neerajadsul/Stagy58/Ortho82Unifiedfirmware/Split82Firmware/Split82Firmware/src/driver_init.c

/**
 * \file
 *
 * \brief Driver initialization.
 *
 (c) 2020 Microchip Technology Inc. and its subsidiaries.

    Subject to your compliance with these terms,you may use this software and
    any derivatives exclusively with Microchip products.It is your responsibility
    to comply with third party license terms applicable to your use of third party
    software (including open source software) that may accompany Microchip software.

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
    IN NO EVENT WILL MICROCHIP BE LIABLE FOR ANY INDIRECT, SPECIAL, PUNITIVE,
    INCIDENTAL OR CONSEQUENTIAL LOSS, DAMAGE, COST OR EXPENSE OF ANY KIND
    WHATSOEVER RELATED TO THE SOFTWARE, HOWEVER CAUSED, EVEN IF MICROCHIP HAS
    BEEN ADVISED OF THE POSSIBILITY OR THE DAMAGES ARE FORESEEABLE. TO THE
    FULLEST EXTENT ALLOWED BY LAW, MICROCHIP'S TOTAL LIABILITY ON ALL CLAIMS IN
    ANY WAY RELATED TO THIS SOFTWARE WILL NOT EXCEED THE AMOUNT OF FEES, IF ANY,
    THAT YOU HAVE PAID DIRECTLY TO MICROCHIP FOR THIS SOFTWARE.
 *
 */

/*
 * Code generated by START.
 *
 * This file will be overwritten when reconfiguring your START project.
 * Please copy examples or other code you want to keep to a separate file
 * to avoid losing it when reconfiguring.
 */

#include "driver_init.h"
#include <system.h>

/* configure pins and initialize registers */
void SLEEP_initialization(void)
{
	SLEEP_init();
}

/* Configure pins and initialize registers */
void USART_KBD_initialization(void)
{

	// Set pin direction to input
	PE2_set_dir(PORT_DIR_IN);

	PE2_set_output_pull_mode(
	    // <y> Output and Pull Configuration
	    // <id> pad_output_pull_config
	    // <PORT_CONFIGURATION_TOTEM"> Totem-pole
	    // <PORT_CONFIGURATION_BUSKEEPER"> Totem-pole with bus-keeper
	    // <PORT_CONFIGURATION_PULLDOWN"> Pull-down
	    // <PORT_CONFIGURATION_PULLUP"> Pull-up
	    // <PORT_CONFIGURATION_WIREDOR"> Wired-OR
	    // <PORT_CONFIGURATION_WIREDAND"> Wired-AND
	    // <PORT_CONFIGURATION_WIREDORPULL"> Wired-OR with pull-down
	    // <PORT_CONFIGURATION_WIREDANDPULL"> Wired-AND with pull-up
	    PORT_CONFIGURATION_TOTEM);

	// Set pin direction to output
	PE3_set_dir(PORT_DIR_OUT);

	PE3_set_level(
	    // <y> Initial level
	    // <id> pad_initial_level
	    // <false"> Low
	    // <true"> High
	    true);

	USART_KBD_init();
}

/* Configure pins and initialize registers */
void USART_USB_initialization(void)
{

	// Set pin direction to input
	PD6_set_dir(PORT_DIR_IN);

	PD6_set_output_pull_mode(
	    // <y> Output and Pull Configuration
	    // <id> pad_output_pull_config
	    // <PORT_CONFIGURATION_TOTEM"> Totem-pole
	    // <PORT_CONFIGURATION_BUSKEEPER"> Totem-pole with bus-keeper
	    // <PORT_CONFIGURATION_PULLDOWN"> Pull-down
	    // <PORT_CONFIGURATION_PULLUP"> Pull-up
	    // <PORT_CONFIGURATION_WIREDOR"> Wired-OR
	    // <PORT_CONFIGURATION_WIREDAND"> Wired-AND
	    // <PORT_CONFIGURATION_WIREDORPULL"> Wired-OR with pull-down
	    // <PORT_CONFIGURATION_WIREDANDPULL"> Wired-AND with pull-up
	    PORT_CONFIGURATION_TOTEM);

	// Set pin direction to output
	PD7_set_dir(PORT_DIR_OUT);

	PD7_set_level(
	    // <y> Initial level
	    // <id> pad_initial_level
	    // <false"> Low
	    // <true"> High
	    false);

	USART_USB_init();
}

/**
 * \brief System initialization
 */
void system_init()
{
	mcu_init();

	/* PORT setting on PB2 */

	// Set pin direction to input
	IS_LEFT_set_dir(PORT_DIR_IN);

	IS_LEFT_set_output_pull_mode(
	    // <y> Output and Pull Configuration
	    // <id> pad_output_pull_config
	    // <PORT_CONFIGURATION_TOTEM"> Totem-pole
	    // <PORT_CONFIGURATION_BUSKEEPER"> Totem-pole with bus-keeper
	    // <PORT_CONFIGURATION_PULLDOWN"> Pull-down
	    // <PORT_CONFIGURATION_PULLUP"> Pull-up
	    // <PORT_CONFIGURATION_WIREDOR"> Wired-OR
	    // <PORT_CONFIGURATION_WIREDAND"> Wired-AND
	    // <PORT_CONFIGURATION_WIREDORPULL"> Wired-OR with pull-down
	    // <PORT_CONFIGURATION_WIREDANDPULL"> Wired-AND with pull-up
	    PORT_CONFIGURATION_TOTEM);

	/* PORT setting on PB3 */

	// Set pin direction to output
	USER_LED_set_dir(PORT_DIR_OUT);

	USER_LED_set_level(
	    // <y> Initial level
	    // <id> pad_initial_level
	    // <false"> Low
	    // <true"> High
	    false);

	/* PORT setting on PC0 */

	// Set pin direction to output
	COL_0_set_dir(PORT_DIR_OUT);

	COL_0_set_level(
	    // <y> Initial level
	    // <id> pad_initial_level
	    // <false"> Low
	    // <true"> High
	    false);

	/* PORT setting on PC1 */

	// Set pin direction to output
	COL_1_set_dir(PORT_DIR_OUT);

	COL_1_set_level(
	    // <y> Initial level
	    // <id> pad_initial_level
	    // <false"> Low
	    // <true"> High
	    true);

	/* PORT setting on PC2 */

	// Set pin direction to output
	COL_2_set_dir(PORT_DIR_OUT);

	COL_2_set_level(
	    // <y> Initial level
	    // <id> pad_initial_level
	    // <false"> Low
	    // <true"> High
	    false);

	/* PORT setting on PC3 */

	// Set pin direction to output
	COL_3_set_dir(PORT_DIR_OUT);

	COL_3_set_level(
	    // <y> Initial level
	    // <id> pad_initial_level
	    // <false"> Low
	    // <true"> High
	    false);

	/* PORT setting on PC4 */

	// Set pin direction to output
	COL_4_set_dir(PORT_DIR_OUT);

	COL_4_set_level(
	    // <y> Initial level
	    // <id> pad_initial_level
	    // <false"> Low
	    // <true"> High
	    false);

	/* PORT setting on PC5 */

	// Set pin direction to output
	COL_5_set_dir(PORT_DIR_OUT);

	COL_5_set_level(
	    // <y> Initial level
	    // <id> pad_initial_level
	    // <false"> Low
	    // <true"> High
	    false);

	/* PORT setting on PC6 */

	// Set pin direction to output
	COL_6_set_dir(PORT_DIR_OUT);

	COL_6_set_level(
	    // <y> Initial level
	    // <id> pad_initial_level
	    // <false"> Low
	    // <true"> High
	    false);

	/* PORT setting on PD0 */

	// Set pin direction to input
	ROW_0_set_dir(PORT_DIR_IN);

	ROW_0_set_output_pull_mode(
	    // <y> Output and Pull Configuration
	    // <id> pad_output_pull_config
	    // <PORT_CONFIGURATION_TOTEM"> Totem-pole
	    // <PORT_CONFIGURATION_BUSKEEPER"> Totem-pole with bus-keeper
	    // <PORT_CONFIGURATION_PULLDOWN"> Pull-down
	    // <PORT_CONFIGURATION_PULLUP"> Pull-up
	    // <PORT_CONFIGURATION_WIREDOR"> Wired-OR
	    // <PORT_CONFIGURATION_WIREDAND"> Wired-AND
	    // <PORT_CONFIGURATION_WIREDORPULL"> Wired-OR with pull-down
	    // <PORT_CONFIGURATION_WIREDANDPULL"> Wired-AND with pull-up
	    PORT_CONFIGURATION_PULLDOWN);

	/* PORT setting on PD1 */

	// Set pin direction to input
	ROW_1_set_dir(PORT_DIR_IN);

	ROW_1_set_output_pull_mode(
	    // <y> Output and Pull Configuration
	    // <id> pad_output_pull_config
	    // <PORT_CONFIGURATION_TOTEM"> Totem-pole
	    // <PORT_CONFIGURATION_BUSKEEPER"> Totem-pole with bus-keeper
	    // <PORT_CONFIGURATION_PULLDOWN"> Pull-down
	    // <PORT_CONFIGURATION_PULLUP"> Pull-up
	    // <PORT_CONFIGURATION_WIREDOR"> Wired-OR
	    // <PORT_CONFIGURATION_WIREDAND"> Wired-AND
	    // <PORT_CONFIGURATION_WIREDORPULL"> Wired-OR with pull-down
	    // <PORT_CONFIGURATION_WIREDANDPULL"> Wired-AND with pull-up
	    PORT_CONFIGURATION_PULLDOWN);

	/* PORT setting on PD2 */

	// Set pin direction to input
	ROW_2_set_dir(PORT_DIR_IN);

	ROW_2_set_output_pull_mode(
	    // <y> Output and Pull Configuration
	    // <id> pad_output_pull_config
	    // <PORT_CONFIGURATION_TOTEM"> Totem-pole
	    // <PORT_CONFIGURATION_BUSKEEPER"> Totem-pole with bus-keeper
	    // <PORT_CONFIGURATION_PULLDOWN"> Pull-down
	    // <PORT_CONFIGURATION_PULLUP"> Pull-up
	    // <PORT_CONFIGURATION_WIREDOR"> Wired-OR
	    // <PORT_CONFIGURATION_WIREDAND"> Wired-AND
	    // <PORT_CONFIGURATION_WIREDORPULL"> Wired-OR with pull-down
	    // <PORT_CONFIGURATION_WIREDANDPULL"> Wired-AND with pull-up
	    PORT_CONFIGURATION_PULLDOWN);

	/* PORT setting on PD3 */

	// Set pin direction to input
	ROW_3_set_dir(PORT_DIR_IN);

	ROW_3_set_output_pull_mode(
	    // <y> Output and Pull Configuration
	    // <id> pad_output_pull_config
	    // <PORT_CONFIGURATION_TOTEM"> Totem-pole
	    // <PORT_CONFIGURATION_BUSKEEPER"> Totem-pole with bus-keeper
	    // <PORT_CONFIGURATION_PULLDOWN"> Pull-down
	    // <PORT_CONFIGURATION_PULLUP"> Pull-up
	    // <PORT_CONFIGURATION_WIREDOR"> Wired-OR
	    // <PORT_CONFIGURATION_WIREDAND"> Wired-AND
	    // <PORT_CONFIGURATION_WIREDORPULL"> Wired-OR with pull-down
	    // <PORT_CONFIGURATION_WIREDANDPULL"> Wired-AND with pull-up
	    PORT_CONFIGURATION_PULLDOWN);

	/* PORT setting on PD4 */

	// Set pin direction to input
	ROW_4_set_dir(PORT_DIR_IN);

	ROW_4_set_output_pull_mode(
	    // <y> Output and Pull Configuration
	    // <id> pad_output_pull_config
	    // <PORT_CONFIGURATION_TOTEM"> Totem-pole
	    // <PORT_CONFIGURATION_BUSKEEPER"> Totem-pole with bus-keeper
	    // <PORT_CONFIGURATION_PULLDOWN"> Pull-down
	    // <PORT_CONFIGURATION_PULLUP"> Pull-up
	    // <PORT_CONFIGURATION_WIREDOR"> Wired-OR
	    // <PORT_CONFIGURATION_WIREDAND"> Wired-AND
	    // <PORT_CONFIGURATION_WIREDORPULL"> Wired-OR with pull-down
	    // <PORT_CONFIGURATION_WIREDANDPULL"> Wired-AND with pull-up
	    PORT_CONFIGURATION_PULLDOWN);

	/* PORT setting on PD5 */

	// Set pin direction to input
	ROW_F_set_dir(PORT_DIR_IN);

	ROW_F_set_output_pull_mode(
	    // <y> Output and Pull Configuration
	    // <id> pad_output_pull_config
	    // <PORT_CONFIGURATION_TOTEM"> Totem-pole
	    // <PORT_CONFIGURATION_BUSKEEPER"> Totem-pole with bus-keeper
	    // <PORT_CONFIGURATION_PULLDOWN"> Pull-down
	    // <PORT_CONFIGURATION_PULLUP"> Pull-up
	    // <PORT_CONFIGURATION_WIREDOR"> Wired-OR
	    // <PORT_CONFIGURATION_WIREDAND"> Wired-AND
	    // <PORT_CONFIGURATION_WIREDORPULL"> Wired-OR with pull-down
	    // <PORT_CONFIGURATION_WIREDANDPULL"> Wired-AND with pull-up
	    PORT_CONFIGURATION_PULLDOWN);

	OSC_init();

	CLK_init();

	PMIC_init();

	SLEEP_initialization();

	USART_KBD_initialization();

	USART_USB_initialization();
}
