neerajadsul/Stagy58/Ortho82Unifiedfirmware/Split82Firmware/Split82Firmware/src/usart_basic.c

/**
 * \file
 *
 * \brief USART basic driver.
 *
 (c) 2020 Microchip Technology Inc. and its subsidiaries.

    Subject to your compliance with these terms,you may use this software and
    any derivatives exclusively with Microchip products.It is your responsibility
    to comply with third party license terms applicable to your use of third party
    software (including open source software) that may accompany Microchip software.

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
    IN NO EVENT WILL MICROCHIP BE LIABLE FOR ANY INDIRECT, SPECIAL, PUNITIVE,
    INCIDENTAL OR CONSEQUENTIAL LOSS, DAMAGE, COST OR EXPENSE OF ANY KIND
    WHATSOEVER RELATED TO THE SOFTWARE, HOWEVER CAUSED, EVEN IF MICROCHIP HAS
    BEEN ADVISED OF THE POSSIBILITY OR THE DAMAGES ARE FORESEEABLE. TO THE
    FULLEST EXTENT ALLOWED BY LAW, MICROCHIP'S TOTAL LIABILITY ON ALL CLAIMS IN
    ANY WAY RELATED TO THIS SOFTWARE WILL NOT EXCEED THE AMOUNT OF FEES, IF ANY,
    THAT YOU HAVE PAID DIRECTLY TO MICROCHIP FOR THIS SOFTWARE.
 *
 */

/**
 * \defgroup doc_driver_usart_basic USART Basic
 * \ingroup doc_driver_usart
 *
 * \section doc_driver_usart_basic_rev Revision History
 * - v0.0.0.1 Initial Commit
 *
 *@{
 */
#include <compiler.h>
#include <clock_config.h>
#include <usart_basic.h>
#include <atomic.h>

/* Static Variables holding the ringbuffer used in IRQ mode */
static uint8_t          USART_KBD_rxbuf[USART_KBD_RX_BUFFER_SIZE];
static volatile uint8_t USART_KBD_rx_head;
static volatile uint8_t USART_KBD_rx_tail;
static volatile uint8_t USART_KBD_rx_elements;
static uint8_t          USART_KBD_txbuf[USART_KBD_TX_BUFFER_SIZE];
static volatile uint8_t USART_KBD_tx_head;
static volatile uint8_t USART_KBD_tx_tail;
static volatile uint8_t USART_KBD_tx_elements;

void USART_KBD_default_rx_isr_cb(void);
void (*USART_KBD_rx_isr_cb)(void) = &USART_KBD_default_rx_isr_cb;
void USART_KBD_default_udre_isr_cb(void);
void (*USART_KBD_udre_isr_cb)(void) = &USART_KBD_default_udre_isr_cb;

void USART_KBD_default_rx_isr_cb(void)
{
	uint8_t data;
	uint8_t tmphead;

	/* Read the received data */
	data = USARTE0.DATA;
	/* Calculate buffer index */
	tmphead = (USART_KBD_rx_head + 1) & USART_KBD_RX_BUFFER_MASK;

	if (tmphead == USART_KBD_rx_tail) {
		/* ERROR! Receive buffer overflow */
	} else {
		/* Store new index */
		USART_KBD_rx_head = tmphead;

		/* Store received data in buffer */
		USART_KBD_rxbuf[tmphead] = data;
		USART_KBD_rx_elements++;
	}
}

void USART_KBD_default_udre_isr_cb(void)
{
	uint8_t tmptail;

	/* Check if all data is transmitted */
	if (USART_KBD_tx_elements != 0) {
		/* Calculate buffer index */
		tmptail = (USART_KBD_tx_tail + 1) & USART_KBD_TX_BUFFER_MASK;
		/* Store new index */
		USART_KBD_tx_tail = tmptail;
		/* Start transmission */
		USARTE0.DATA = USART_KBD_txbuf[tmptail];
		USART_KBD_tx_elements--;
	}

	if (USART_KBD_tx_elements == 0) {
		/* Disable UDRE interrupt */
		USARTE0.CTRLA &= ~(USART_DREINTLVL_gm);
	}
}

/**
 * \brief Set call back function for USART_KBD
 *
 * \param[in] cb The call back function to set
 *
 * \param[in] type The type of ISR to be set
 *
 * \return Nothing
 */
void USART_KBD_set_ISR_cb(usart_cb_t cb, usart_cb_type_t type)
{
	switch (type) {
	case RX_CB:
		USART_KBD_rx_isr_cb = cb;
		break;
	case UDRE_CB:
		USART_KBD_udre_isr_cb = cb;
		break;
	default:
		// do nothing
		break;
	}
}

/* Interrupt service routine for RX complete */
ISR(USARTE0_RXC_vect)
{
	if (USART_KBD_rx_isr_cb != NULL)
		(*USART_KBD_rx_isr_cb)();
}

/* Interrupt service routine for Data Register Empty */
ISR(USARTE0_DRE_vect)
{
	if (USART_KBD_udre_isr_cb != NULL)
		(*USART_KBD_udre_isr_cb)();
}

bool USART_KBD_is_tx_ready()
{
	return (USART_KBD_tx_elements != USART_KBD_TX_BUFFER_SIZE);
}

bool USART_KBD_is_rx_ready()
{
	return (USART_KBD_rx_elements != 0);
}

bool USART_KBD_is_tx_busy()
{
	return (!(USARTE0.STATUS & USART_TXCIF_bm));
}

/**
 * \brief Read one character from USART_KBD
 *
 * Function will block if a character is not available.
 *
 * \return Data read from the USART_KBD module
 */
uint8_t USART_KBD_read(void)
{
	uint8_t tmptail;

	/* Wait for incoming data */
	while (USART_KBD_rx_elements == 0)
		;
	/* Calculate buffer index */
	tmptail = (USART_KBD_rx_tail + 1) & USART_KBD_RX_BUFFER_MASK;
	/* Store new index */
	USART_KBD_rx_tail = tmptail;
	ENTER_CRITICAL(R);
	USART_KBD_rx_elements--;
	EXIT_CRITICAL(R);

	/* Return data */
	return USART_KBD_rxbuf[tmptail];
}

/**
 * \brief Write one character to USART_KBD
 *
 * Function will block until a character can be accepted.
 *
 * \param[in] data The character to write to the USART
 *
 * \return Nothing
 */
void USART_KBD_write(const uint8_t data)
{
	uint8_t tmphead;

	/* Calculate buffer index */
	tmphead = (USART_KBD_tx_head + 1) & USART_KBD_TX_BUFFER_MASK;
	/* Wait for free space in buffer */
	while (USART_KBD_tx_elements == USART_KBD_TX_BUFFER_SIZE)
		;
	/* Store data in buffer */
	USART_KBD_txbuf[tmphead] = data;
	/* Store new index */
	USART_KBD_tx_head = tmphead;
	ENTER_CRITICAL(W);
	USART_KBD_tx_elements++;
	EXIT_CRITICAL(W);
	/* Enable UDRE interrupt */
	USARTE0.CTRLA |= USART_DREINTLVL_LO_gc;
}

/**
 * \brief Initialize USART interface
 * If module is configured to disabled state, the clock to the USART is disabled
 * if this is supported by the device's clock system.
 *
 * \return Initialization status.
 * \retval 0 the USART init was successful
 * \retval 1 the USART init was not successful
 */
int8_t USART_KBD_init()
{

	int8_t   exp;
	uint32_t div;
	uint32_t limit;
	uint32_t ratio;
	uint32_t min_rate;
	uint32_t max_rate;

	uint32_t cpu_hz = F_CPU;
	uint32_t baud   = 115200;

	/*
	 * Check if the hardware supports the given baud rate
	 */
	/* 8 = (2^0) * 8 * (2^0) = (2^BSCALE_MIN) * 8 * (BSEL_MIN) */
	max_rate = cpu_hz / 8;
	/* 4194304 = (2^7) * 8 * (2^12) = (2^BSCALE_MAX) * 8 * (BSEL_MAX+1) */
	min_rate = cpu_hz / 4194304;

	/* double speed is disabled. */
	max_rate /= 2;
	min_rate /= 2;

	if ((baud > max_rate) || (baud < min_rate)) {
		/* the hardware doesn't supports the given baud rate */
		return -1;
	}

	/* double speed is disabled. */
	baud *= 2;

	/* Find the lowest possible exponent. */
	limit = 0xfffU >> 4;
	ratio = cpu_hz / baud;

	for (exp = -7; exp < 7; exp++) {
		if (ratio < limit) {
			break;
		}

		limit <<= 1;

		if (exp < -3) {
			limit |= 1;
		}
	}

	/*
	 * Depending on the value of exp, scale either the input frequency or
	 * the target baud rate. By always scaling upwards, we never introduce
	 * any additional inaccuracy.
	 *
	 * We are including the final divide-by-8 (aka. right-shift-by-3) in
	 * this operation as it ensures that we never exceeed 2**32 at any
	 * point.
	 *
	 * The formula for calculating BSEL is slightly different when exp is
	 * negative than it is when exp is positive.
	 */
	if (exp < 0) {
		/* We are supposed to subtract 1, then apply BSCALE. We want to
		 * apply BSCALE first, so we need to turn everything inside the
		 * parenthesis into a single fractional expression.
		 */
		cpu_hz -= 8 * baud;

		/* If we end up with a left-shift after taking the final
		 * divide-by-8 into account, do the shift before the divide.
		 * Otherwise, left-shift the denominator instead (effectively
		 * resulting in an overall right shift.)
		 */
		if (exp <= -3) {
			div = ((cpu_hz << (-exp - 3)) + baud / 2) / baud;
		} else {
			baud <<= exp + 3;
			div = (cpu_hz + baud / 2) / baud;
		}
	} else {
		/* We will always do a right shift in this case, but we need to
		 * shift three extra positions because of the divide-by-8.
		 */
		baud <<= exp + 3;
		div = (cpu_hz + baud / 2) / baud - 1;
	}

	USARTE0.BAUDCTRLB = (uint8_t)(((div >> 8) & 0X0F) | (exp << 4));
	USARTE0.BAUDCTRLA = (uint8_t)div;

	USARTE0.CTRLA = USART_RXCINTLVL_LO_gc    /* Low Level */
	                | USART_TXCINTLVL_OFF_gc /* Off */
	                | USART_DREINTLVL_LO_gc; /* Low Level */

	// USARTE0.CTRLC = USART_PMODE_DISABLED_gc /* No Parity */
	//		 | 0 << USART_SBMODE_bp /* Stop Bit Mode: disabled */
	//		 | USART_CHSIZE_8BIT_gc /* Character size: 8 bit */
	//		 | 0 << USART_CHSIZE2_bp /* SPI Master Mode, Data Order: disabled */
	//		 | 1 << USART_CHSIZE1_bp /* SPI Master Mode, Clock Phase: enabled */
	//		 | USART_CMODE_ASYNCHRONOUS_gc; /* Async IRQ Mode */

	USARTE0.CTRLB = 0 << USART_CLK2X_bp   /* Double transmission speed: disabled */
	                | 0 << USART_MPCM_bp  /* Multi-processor Communication Mode: disabled */
	                | 1 << USART_RXEN_bp  /* Receiver Enable: enabled */
	                | 1 << USART_TXEN_bp; /* Transmitter Enable: enabled */

	uint8_t x;

	/* Initialize ringbuffers */
	x = 0;

	USART_KBD_rx_tail     = x;
	USART_KBD_rx_head     = x;
	USART_KBD_rx_elements = x;
	USART_KBD_tx_tail     = x;
	USART_KBD_tx_head     = x;
	USART_KBD_tx_elements = x;

	return 0;
}

/**
 * \brief Enable RX and TX in USART_KBD
 * 1. If supported by the clock system, enables the clock to the USART
 * 2. Enables the USART module by setting the RX and TX enable-bits in the USART control register
 *
 * \return Nothing
 */
void USART_KBD_enable()
{
	USARTE0.CTRLB |= USART_RXEN_bm | USART_TXEN_bm;
}

/**
 * \brief Enable RX in USART_KBD
 * 1. If supported by the clock system, enables the clock to the USART
 * 2. Enables the USART module by setting the RX enable-bit in the USART control register
 *
 * \return Nothing
 */
void USART_KBD_enable_rx()
{
	USARTE0.CTRLB |= USART_RXEN_bm;
}

/**
 * \brief Enable TX in USART_KBD
 * 1. If supported by the clock system, enables the clock to the USART
 * 2. Enables the USART module by setting the TX enable-bit in the USART control register
 *
 * \return Nothing
 */
void USART_KBD_enable_tx()
{
	USARTE0.CTRLB |= USART_TXEN_bm;
}

/**
 * \brief Disable USART_KBD
 * 1. Disables the USART module by clearing the enable-bit(s) in the USART control register
 * 2. If supported by the clock system, disables the clock to the USART
 *
 * \return Nothing
 */
void USART_KBD_disable()
{
	USARTE0.CTRLB &= ~(USART_RXEN_bm | USART_TXEN_bm);
}

/**
 * \brief Get recieved data from USART_KBD
 *
 * \return Data register from USART_KBD module
 */
uint8_t USART_KBD_get_data()
{
	return USARTE0.DATA;
}

#include <stdio.h>

#if defined(__GNUC__)

int USART_USB_printCHAR(char character, FILE *stream)
{
	USART_USB_write(character);
	return 0;
}

FILE USART_USB_stream = FDEV_SETUP_STREAM(USART_USB_printCHAR, NULL, _FDEV_SETUP_WRITE);

#elif defined(__ICCAVR__)

int putchar(int outChar)
{
	USART_0_write(outChar);
	return outChar;
}
#endif

/**
 * \brief Initialize USART interface
 * If module is configured to disabled state, the clock to the USART is disabled
 * if this is supported by the device's clock system.
 *
 * \return Initialization status.
 * \retval 0 the USART init was successful
 * \retval 1 the USART init was not successful
 */
int8_t USART_USB_init()
{

	int8_t   exp;
	uint32_t div;
	uint32_t limit;
	uint32_t ratio;
	uint32_t min_rate;
	uint32_t max_rate;

	uint32_t cpu_hz = F_CPU;
	uint32_t baud   = 9600;

	/*
	 * Check if the hardware supports the given baud rate
	 */
	/* 8 = (2^0) * 8 * (2^0) = (2^BSCALE_MIN) * 8 * (BSEL_MIN) */
	max_rate = cpu_hz / 8;
	/* 4194304 = (2^7) * 8 * (2^12) = (2^BSCALE_MAX) * 8 * (BSEL_MAX+1) */
	min_rate = cpu_hz / 4194304;

	/* double speed is disabled. */
	max_rate /= 2;
	min_rate /= 2;

	if ((baud > max_rate) || (baud < min_rate)) {
		/* the hardware doesn't supports the given baud rate */
		return -1;
	}

	/* double speed is disabled. */
	baud *= 2;

	/* Find the lowest possible exponent. */
	limit = 0xfffU >> 4;
	ratio = cpu_hz / baud;

	for (exp = -7; exp < 7; exp++) {
		if (ratio < limit) {
			break;
		}

		limit <<= 1;

		if (exp < -3) {
			limit |= 1;
		}
	}

	/*
	 * Depending on the value of exp, scale either the input frequency or
	 * the target baud rate. By always scaling upwards, we never introduce
	 * any additional inaccuracy.
	 *
	 * We are including the final divide-by-8 (aka. right-shift-by-3) in
	 * this operation as it ensures that we never exceeed 2**32 at any
	 * point.
	 *
	 * The formula for calculating BSEL is slightly different when exp is
	 * negative than it is when exp is positive.
	 */
	if (exp < 0) {
		/* We are supposed to subtract 1, then apply BSCALE. We want to
		 * apply BSCALE first, so we need to turn everything inside the
		 * parenthesis into a single fractional expression.
		 */
		cpu_hz -= 8 * baud;

		/* If we end up with a left-shift after taking the final
		 * divide-by-8 into account, do the shift before the divide.
		 * Otherwise, left-shift the denominator instead (effectively
		 * resulting in an overall right shift.)
		 */
		if (exp <= -3) {
			div = ((cpu_hz << (-exp - 3)) + baud / 2) / baud;
		} else {
			baud <<= exp + 3;
			div = (cpu_hz + baud / 2) / baud;
		}
	} else {
		/* We will always do a right shift in this case, but we need to
		 * shift three extra positions because of the divide-by-8.
		 */
		baud <<= exp + 3;
		div = (cpu_hz + baud / 2) / baud - 1;
	}

	USARTD1.BAUDCTRLB = (uint8_t)(((div >> 8) & 0X0F) | (exp << 4));
	USARTD1.BAUDCTRLA = (uint8_t)div;

	// USARTD1.CTRLC = USART_PMODE_DISABLED_gc /* No Parity */
	//		 | 0 << USART_SBMODE_bp /* Stop Bit Mode: disabled */
	//		 | USART_CHSIZE_8BIT_gc /* Character size: 8 bit */
	//		 | 0 << USART_CHSIZE2_bp /* SPI Master Mode, Data Order: disabled */
	//		 | 1 << USART_CHSIZE1_bp /* SPI Master Mode, Clock Phase: enabled */
	//		 | USART_CMODE_ASYNCHRONOUS_gc; /* Async Polled Mode */

	USARTD1.CTRLB = 0 << USART_CLK2X_bp   /* Double transmission speed: disabled */
	                | 0 << USART_MPCM_bp  /* Multi-processor Communication Mode: disabled */
	                | 1 << USART_RXEN_bp  /* Receiver Enable: enabled */
	                | 1 << USART_TXEN_bp; /* Transmitter Enable: enabled */

#if defined(__GNUC__)
	stdout = &USART_USB_stream;
#endif

	return 0;
}

/**
 * \brief Enable RX and TX in USART_USB
 * 1. If supported by the clock system, enables the clock to the USART
 * 2. Enables the USART module by setting the RX and TX enable-bits in the USART control register
 *
 * \return Nothing
 */
void USART_USB_enable()
{
	USARTD1.CTRLB |= USART_RXEN_bm | USART_TXEN_bm;
}

/**
 * \brief Enable RX in USART_USB
 * 1. If supported by the clock system, enables the clock to the USART
 * 2. Enables the USART module by setting the RX enable-bit in the USART control register
 *
 * \return Nothing
 */
void USART_USB_enable_rx()
{
	USARTD1.CTRLB |= USART_RXEN_bm;
}

/**
 * \brief Enable TX in USART_USB
 * 1. If supported by the clock system, enables the clock to the USART
 * 2. Enables the USART module by setting the TX enable-bit in the USART control register
 *
 * \return Nothing
 */
void USART_USB_enable_tx()
{
	USARTD1.CTRLB |= USART_TXEN_bm;
}

/**
 * \brief Disable USART_USB
 * 1. Disables the USART module by clearing the enable-bit(s) in the USART control register
 * 2. If supported by the clock system, disables the clock to the USART
 *
 * \return Nothing
 */
void USART_USB_disable()
{
	USARTD1.CTRLB &= ~(USART_RXEN_bm | USART_TXEN_bm);
}

/**
 * \brief Get recieved data from USART_USB
 *
 * \return Data register from USART_USB module
 */
uint8_t USART_USB_get_data()
{
	return USARTD1.DATA;
}

/**
 * \brief Check if the usart can accept data to be transmitted
 *
 * \return The status of USART TX data ready check
 * \retval false The USART can not receive data to be transmitted
 * \retval true The USART can receive data to be transmitted
 */
bool USART_USB_is_tx_ready()
{
	return (USARTD1.STATUS & USART_DREIF_bm);
}

/**
 * \brief Check if the USART has received data
 *
 * \return The status of USART RX data ready check
 * \retval true The USART has received data
 * \retval false The USART has not received data
 */
bool USART_USB_is_rx_ready()
{
	return (USARTD1.STATUS & USART_RXCIF_bm);
}

/**
 * \brief Check if USART_USB data is transmitted
 *
 * \return Receiver ready status
 * \retval true  Data is not completely shifted out of the shift register
 * \retval false Data completely shifted out if the USART shift register
 */
bool USART_USB_is_tx_busy()
{
	return (!(USARTD1.STATUS & USART_TXCIF_bm));
}

/**
 * \brief Read one character from USART_USB
 *
 * Function will block if a character is not available.
 *
 * \return Data read from the USART_USB module
 */
uint8_t USART_USB_read()
{
	while (!(USARTD1.STATUS & USART_RXCIF_bm))
		;
	return USARTD1.DATA;
}

/**
 * \brief Write one character to USART_USB
 *
 * Function will block until a character can be accepted.
 *
 * \param[in] data The character to write to the USART
 *
 * \return Nothing
 */
void USART_USB_write(const uint8_t data)
{
	while (!(USARTD1.STATUS & USART_DREIF_bm))
		;
	USARTD1.DATA = data;
}
