neerajadsul/Stagy58/Ortho82Unifiedfirmware/Split82Firmware/Split82Firmware/src/version.c

#include <stdio.h>
#include <string.h>
#include "version.h"

const int MAJOR = 1;
const int MINOR = 0;
const int PATCH = 0;

const char TIMESTAMP[20] = "2024-11-30_13:34:53";

char* get_semantic_version()
{
	static char sem_ver[30];
	sprintf(sem_ver, "%d.%d.%d_%s", MAJOR, MINOR, PATCH, TIMESTAMP);
	//strcat(sem_ver, TIMESTAMP);
	return sem_ver;
}
