neerajadsul/Stagy58/Ortho82Unifiedfirmware/Split82Firmware/Split82Firmware/include/keycodes.h

/*
 * keycodes.c
 *
 * Created: 22/11/2024 16:22:31
 *  Author: neeraj
 */ 

// Modifier Keys
#define LEFT_CTRL 0x01
#define LEFT_SHIFT 0x02
#define LEFT_ALT 0x04
#define LEFT_GUI 0x08
#define RIGHT_CTRL 0x10
#define RIGHT_SHIFT 0x20
#define RIGHT_ALT 0x40
#define RIGHT_GUI 0x80

// Key Codes
#define A 0x04
#define B 0x05
#define C 0x06
#define D 0x07
#define E 0x08
#define F 0x09
#define G 0x0A
#define H 0x0B
#define I 0x0C
#define J 0x0D
#define K 0x0E
#define L 0x0F
#define M 0x10
#define N 0x11
#define O 0x12
#define P 0x13
#define Q 0x14
#define R 0x15
#define S 0x16
#define T 0x17
#define U 0x18
#define V 0x19
#define W 0x1A
#define X 0x1B
#define Y 0x1C
#define Z 0x1D
#define ONE 0x1E
#define TWO 0x1F
#define THREE 0x20
#define FOUR 0x21
#define FIVE 0x22
#define SIX 0x23
#define SEVEN 0x24
#define EIGHT 0x25
#define NINE 0x26
#define ZERO 0x27
#define ENTER 0x28
#define ESC 0x29
#define BACKSPACE 0x2A
#define TAB 0x2B
#define SPACE 0x2C
#define MINUS 0x2D
#define EQUAL 0x2E
#define LEFT_BRACE 0x2F
#define RIGHT_BRACE 0x30
#define BACKSLASH 0x31
#define SEMICOLON 0x33
#define QUOTE 0x34
#define TILDE 0x35
#define COMMA 0x36
#define PERIOD 0x37
#define SLASH 0x38
#define CAPS_LOCK 0x39
#define F1 0x3A
#define F2 0x3B
#define F3 0x3C
#define F4 0x3D
#define F5 0x3E
#define F6 0x3F
#define F7 0x40
#define F8 0x41
#define F9 0x42
#define F10 0x43
#define F11 0x44
#define F12 0x45
#define PRINTSCREEN 0x46
#define SCROLL_LOCK 0x47
#define PAUSE 0x48
#define INSERT 0x49
#define HOME 0x4A
#define PAGE_UP 0x4B
#define DELETE 0x4C
#define END 0x4D
#define PAGE_DOWN 0x4E
#define RIGHT 0x4F
#define LEFT 0x50
#define DOWN 0x51
#define UP 0x52
#define NUM_LOCK 0x53
#define NUMPAD_SLASH 0x54
#define NUMPAD_ASTERISK 0x55
#define NUMPAD_MINUS 0x56
#define NUMPAD_PLUS 0x57
#define NUMPAD_ENTER 0x58
#define NUMPAD_1 0x59
#define NUMPAD_2 0x5A
#define NUMPAD_3 0x5B
#define NUMPAD_4 0x5C
#define NUMPAD_5 0x5D
#define NUMPAD_6 0x5E
#define NUMPAD_7 0x5F
#define NUMPAD_8 0x60
#define NUMPAD_9 0x61
#define NUMPAD_0 0x62
#define NUMPAD_PERIOD 0x63
